m-archibald/Brainfuino/documentation/docs/imgs/brainfuino-rev1-1-pcb-top-unpopulated.jpg

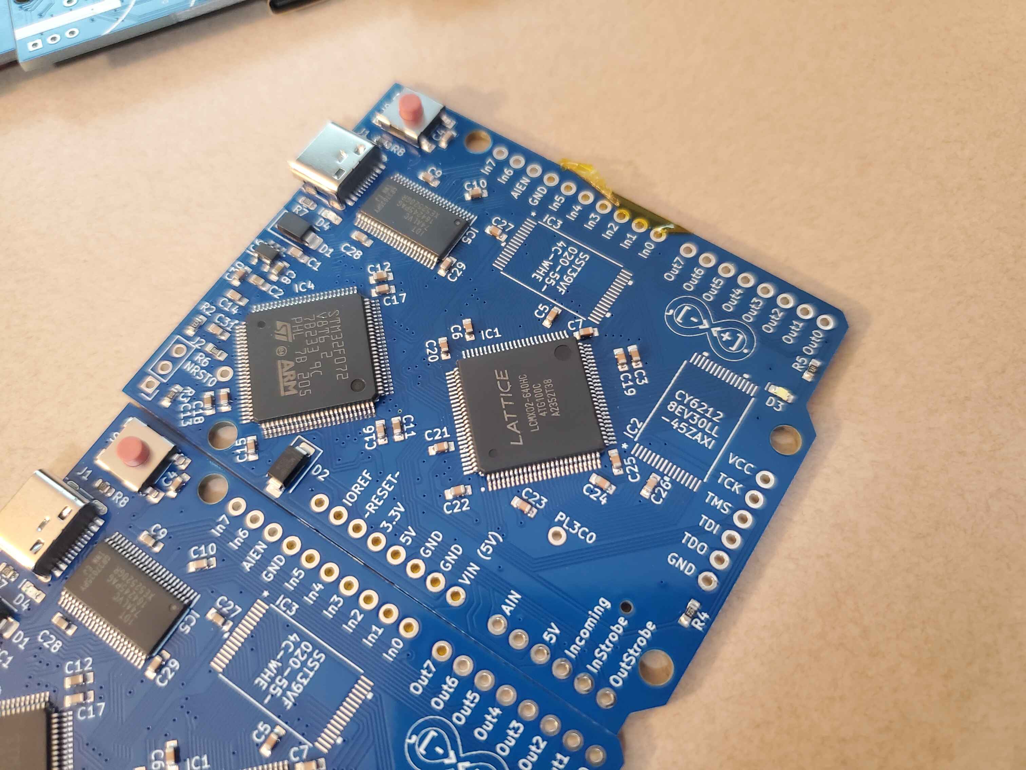
documentation/docs/imgs/brainfuino-rev1-1-pcb-top-unpopulated.jpg
