m-archibald/Brainfuino/documentation/docs/imgs/cubeprogrammer-dfu.png

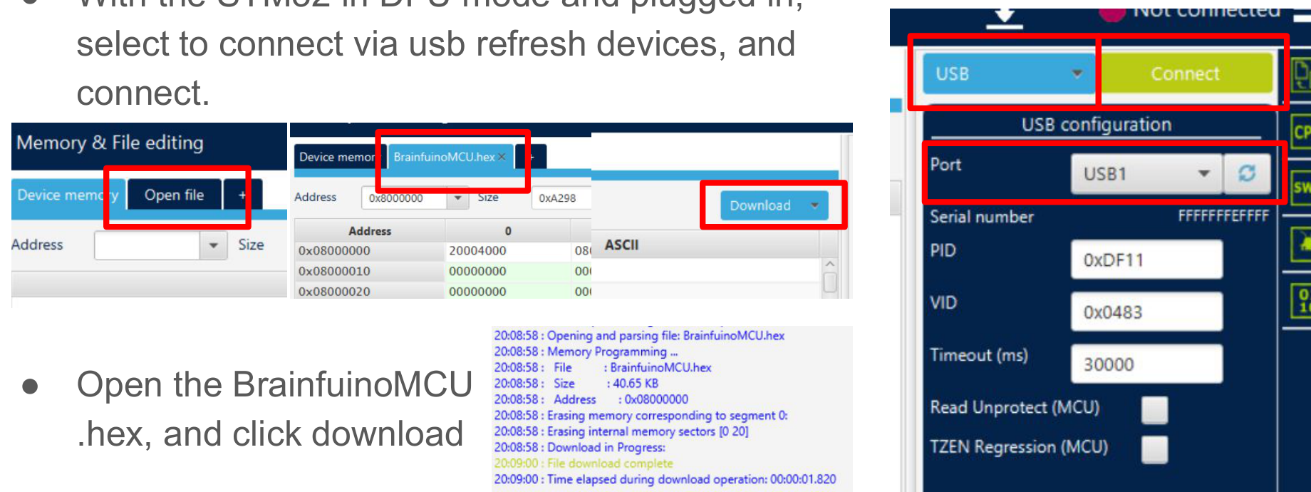
documentation/docs/imgs/cubeprogrammer-dfu.png
