m-archibald/Brainfuino/documentation/docs/imgs/teraterm-paste-code.jpg

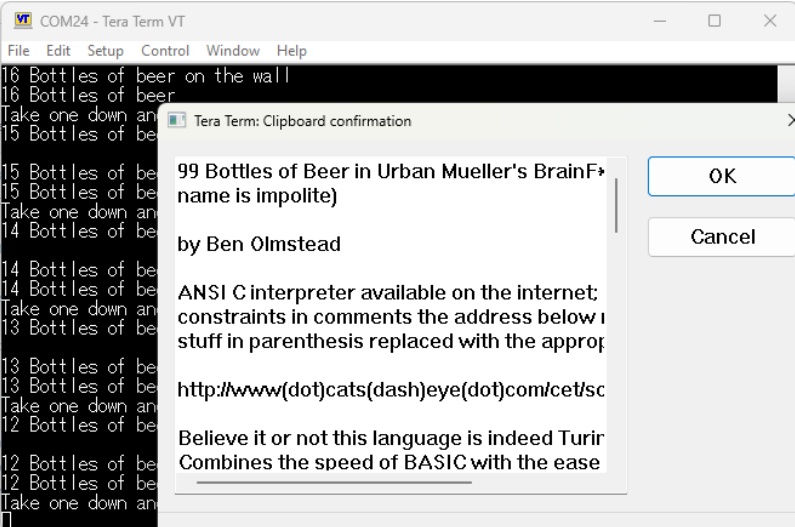
documentation/docs/imgs/teraterm-paste-code.jpg
